RingingResonance/OGP/demodulators/partsRef.png

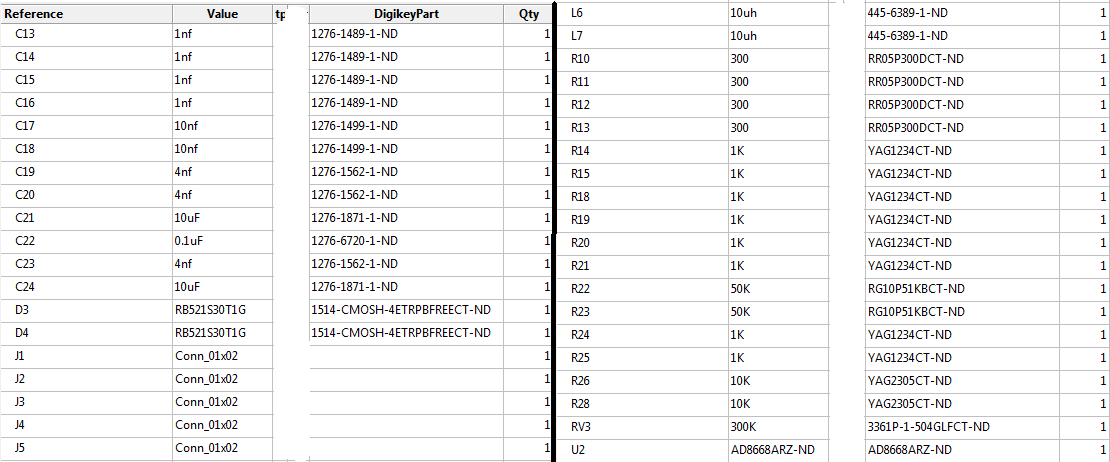
demodulators/partsRef.png
