RingingResonance/OGP/pickups/partsRef.png

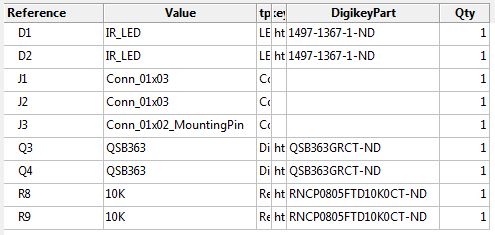
pickups/partsRef.png
