RingingResonance/OGP/powersupply/partsRef.png

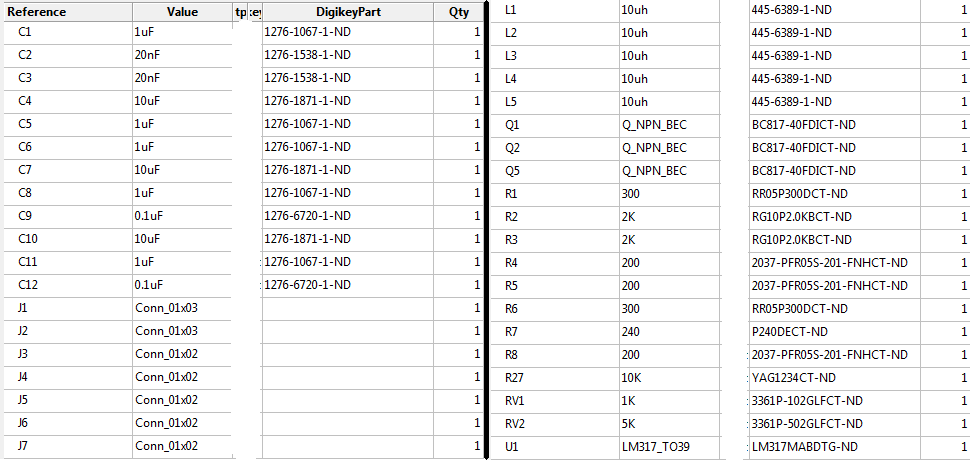
powersupply/partsRef.png
